ryanhowarth/openhand-ble-control/cad/micro controller.SLDPRT

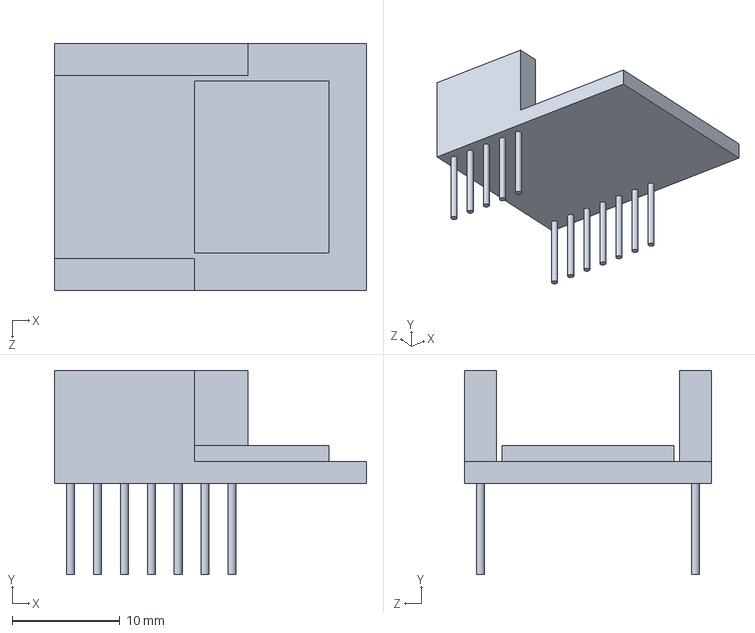
[picture p15: CAD file, 2015-07-24]
cad/micro controller.SLDPRT
29.0 x 19.0 x 23.0 mm
