ryanhowarth/openhand-ble-control/cad/48V to 12V DC to DC converter.SLDPRT

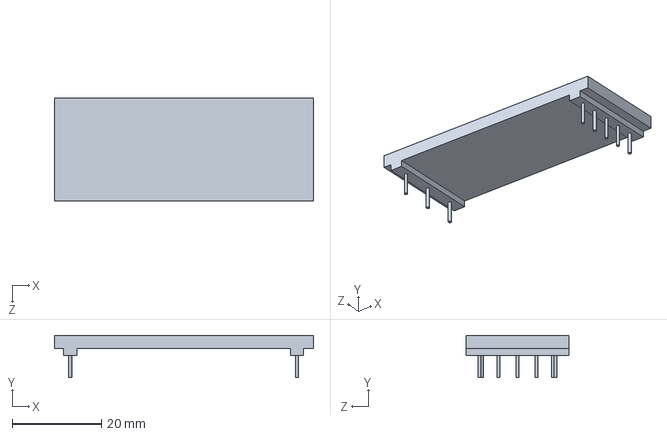
[picture p16: CAD file, 2015-07-24]
cad/48V to 12V DC to DC converter.SLDPRT
58.0 x 9.50 x 23.0 mm
