ryanhowarth/openhand-ble-control/cad/angle bracket.SLDPRT

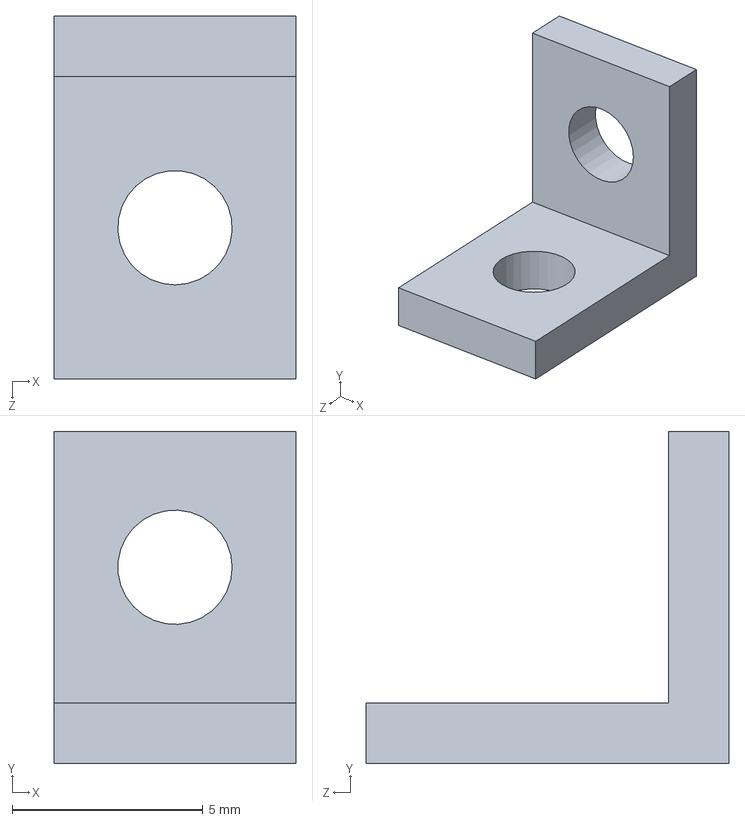
[picture p17: CAD file, 2015-07-24]
cad/angle bracket.SLDPRT
6.35 x 8.71 x 9.53 mm
