ryanhowarth/openhand-ble-control/cad/perf board bottom.SLDPRT

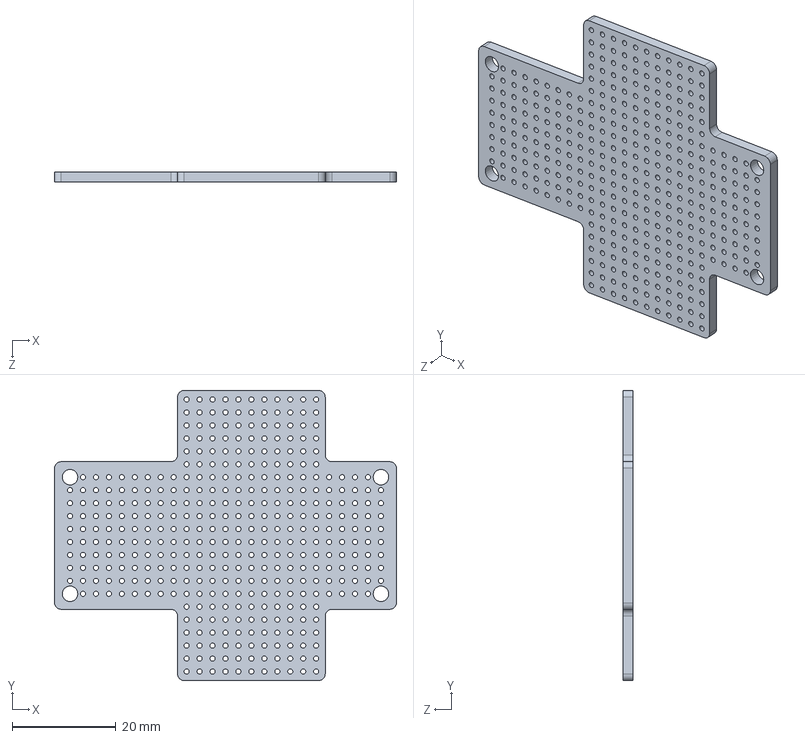
[picture p18: CAD file, 2015-06-29]
cad/perf board bottom.SLDPRT
66.0 x 56.0 x 2.00 mm
