ryanhowarth/openhand-ble-control/cad/m6 standoffs.SLDPRT

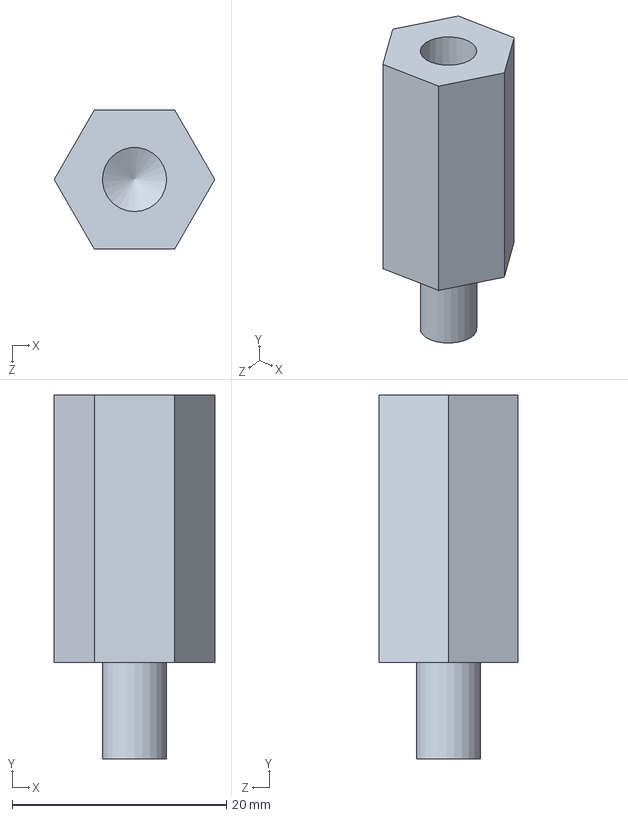
[picture p19: CAD file, 2015-06-23]
cad/m6 standoffs.SLDPRT
15.0 x 34.0 x 13.0 mm
